smartykit/apple1/SmartyKit_Modules_Scheme.sch

## KiCad design SmartyKit_Modules_Scheme.sch (2021-04-29)

Schematic: SmartyKit_Modules_Scheme.sch

Parts:
C1, C2, C3, C4, C5, C6: 22pF; C_0603_1608Metric
C7, C8, C9, C10, C11, C12, C13, C14, C15, C16, C17, C18, C19, C20: 0.1uF; C_0603_1608Metric
D1, D2, D3: Green; LED_0603_1608Metric
D4, D5, D6, D7, D8, D9, D10, D11, D12, D13, D14, D15, D16, D17, D18, D19: Green; LED_D3.0mm
J1, J4, J5, J9, J16, J18, J21, J22, J23, J24, J27, J30, J32, J33, J42, J45, J48, J52, J55, J56: Conn_01x02; PinSocket_1x02_P2.54mm_Vertical_SMD_Pin1Left
J2, J17, J20, J26, J29, J35, J36, J41, J49, J54: Conn_01x08; PinSocket_1x08_P2.54mm_Vertical_SMD_Pin1Left
J3, J13, J14, J15: Conn_01x14; PinSocket_1x14_P2.54mm_Vertical_SMD_Pin1Left
J6, J7, J8, J28, J34, J39, J44, J46, J47: Conn_01x06; PinSocket_1x06_P2.54mm_Vertical_SMD_Pin1Left
J10, J11, J12: Conn_01x07; PinSocket_1x07_P2.54mm_Vertical_SMD_Pin1Left
J19, J40, J53: Conn_01x16; PinSocket_1x16_P2.54mm_Vertical_SMD_Pin1Left
J25: Conn_01x15; PinSocket_1x15_P2.54mm_Vertical_SMD_Pin1Left
J31, J38, J43: Conn_01x04; PinSocket_1x04_P2.54mm_Vertical_SMD_Pin1Left
J37: Conn_01x05; PinSocket_1x05_P2.54mm_Vertical_SMD_Pin1Left
J50, J51, J57: Conn_01x03; PinSocket_1x03_P2.54mm_Vertical_SMD_Pin1Left
R1, R5: 1k; R_0603_1608Metric
R2, R6, R7: 10k; R_0603_1608Metric
R3, R4: 2k2; R_0603_1608Metric
R8, R9, R10, R11: 3k3; R_0603_1608Metric
SW1, SW2: SW_MEC_5E; SW_Push_1P1T_NO_CK_KSC7xxJ
X1: TXC-7C; Oscillator_SMD_TXC_7C-4Pin_5.0x3.2mm
Y1, Y2, Y3: 16Mhz; Crystal_SMD_0603-2Pin_6.0x3.5mm

Notes on the sheet:
MOD5. NAND (R/W)
MOD2. Memory decoder
MOD4. CPU 6502
MOD1. Memory (ROM+RAM)
MOD3. AND (ROM select)
Board 1
Board 2
MOD16. Keyboard connector (PS/2)
MOD11. Keyboard controller
MOD10. Video controller
MOD12. TV controller
MOD14. Shift register
MOD17. Video connector
Board 4
Board 5
Power connector
Board 3
MOD13. Display module
MOD6. Video port
MOD7. BIT7 ports
MOD8. Keyboard port
MOD9. Ports decoder
MOD15. Address&data bus connector (CPU<->Memory)
1MHz clock generator
CPU RESET button
CPU Clock & Reset
Decoupling capacitors
LEDs for tests
ROM
RAM
1 – MOD1. Memory (ROM + RAM) 2 – MOD2. Memory decoder 3 – MOD3. AND gate (ROM select) 4 – MOD4. CPU 5 – MOD5. NAND gate (CPU R/W) 6 – MOD6. Video port 7 – MOD7. BIT7 ports (Kbd7 & Video7) 8 – MOD8. Keyboard port 9 – MOD9. Ports decoder 10 - MOD10. Video controller 11 - MOD11. Keyboard controller 12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
SmartyKit 1 molules list
